vgiauffret/ITII_ELEC_Module_EXT/Code/LoRa/OLED_LoRa_Receive/OLED_LoRa_Receive.ino

#include <splash.h>

#include <SPI.h>
#include <LoRa.h>
#include <Wire.h>
#include "SSD1306.h"
#include "images.h"

#define SCK     5    // GPIO5  -- SX1278's SCK
#define MISO    19   // GPIO19 -- SX1278's MISO
#define MOSI    27   // GPIO27 -- SX1278's MOSI
#define SS      18   // GPIO18 -- SX1278's CS
#define RST     14   // GPIO14 -- SX1278's RESET
#define DI0     26   // GPIO26 -- SX1278's IRQ(Interrupt Request)
#define BAND    868E6

SSD1306 display(0x3c, 21, 22);
String rssi = "RSSI--";
String packSize = "--";
String packet = "";


void loraData() {
  display.clear();
  display.setTextAlignment(TEXT_ALIGN_LEFT);
  display.setFont(ArialMT_Plain_10);
  display.drawString(0 , 15 , "Received " + packSize + " bytes");
  display.drawStringMaxWidth(0 , 26 , 128, packet);
  display.drawString(0, 0, rssi);
  display.display();
  //Serial.println(rssi);
}

void cbk(int packetSize) {
  packet = "";
  packSize = String(packetSize, DEC);
  for (int i = 0; i < packetSize; i++) {
    if (readRegisterCRC(0x3F) == true) {
      packet += (char) LoRa.read();
    }
    else
    {
      display.clear();
      display.setTextAlignment(TEXT_ALIGN_LEFT);
      display.setFont(ArialMT_Plain_10);
      display.drawString(0 , 15 , "Received " + packSize + " bytes");
      display.drawStringMaxWidth(0 , 26 , 128, packet);
      display.drawString(0, 0, "erreur CRC");
      display.display();
      Serial.println(rssi);
      delay(1000);
    }
  }
  rssi = "RSSI " + String(LoRa.packetRssi(), DEC) ;
  loraData();
}

void setup() {
  pinMode(16, OUTPUT);
  digitalWrite(16, LOW);    // set GPIO16 low to reset OLED
  delay(50);
  digitalWrite(16, HIGH); // while OLED is running, must set GPIO16 in high、

  Serial.begin(115200);
  while (!Serial);
  Serial.println();
  Serial.println("LoRa Receiver Callback");
  SPI.begin(SCK, MISO, MOSI, SS);
  LoRa.setPins(SS, RST, DI0);
  if (!LoRa.begin(868E6)) {
    Serial.println("Starting LoRa failed!");
    while (1);
  }
  //LoRa.setSpreadingFactor(7);
  //LoRa.onReceive(cbk);
  LoRa.receive();
  Serial.println("init ok");
  display.init();
  display.flipScreenVertically();
  display.setFont(ArialMT_Plain_10);

  delay(1500);
}

void loop() {
  int packetSize = LoRa.parsePacket();   // onregarde si quelque chose est reçu
  if (packetSize) {
    cbk(packetSize);
    Serial.print(packet);
    if (packet == "HelloYou ") {
      Serial.print("t1");
      delay(10);
      LoRa.beginPacket();
      LoRa.print("Message reçu par 1");
      //delay(100);
      //LoRa.print("Message reçu par 2");
      LoRa.endPacket();
    }
  }
}
